ericboehlke/Resistor-Reader/resistor_pictures/0003.jpg

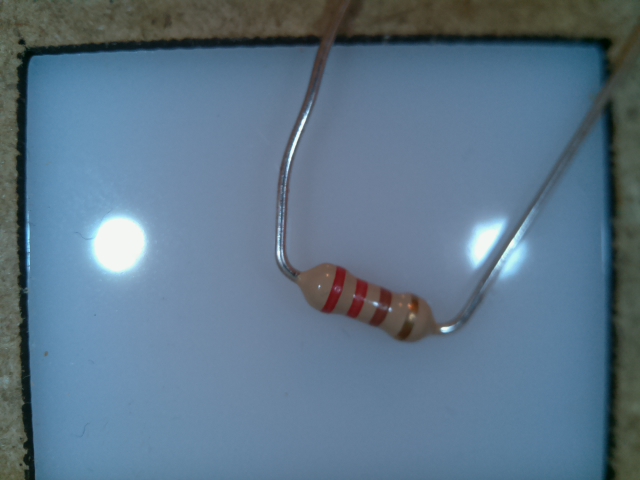
resistor_pictures/0003.jpg
