ericboehlke/Resistor-Reader/resistor_pictures/0000.jpg

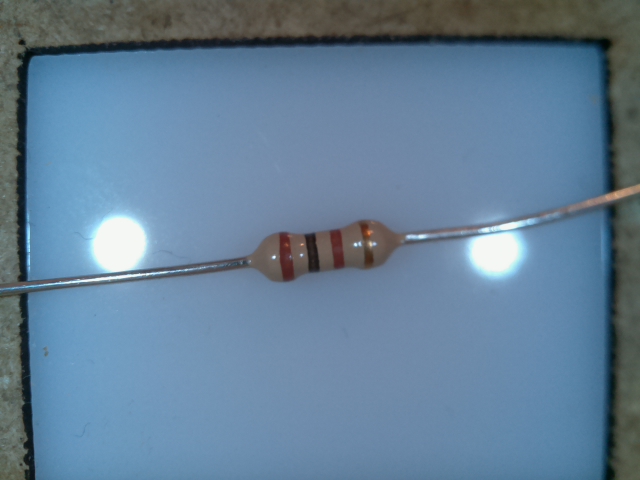
resistor_pictures/0000.jpg
