ericboehlke/Resistor-Reader/resistor_pictures/0002.jpg

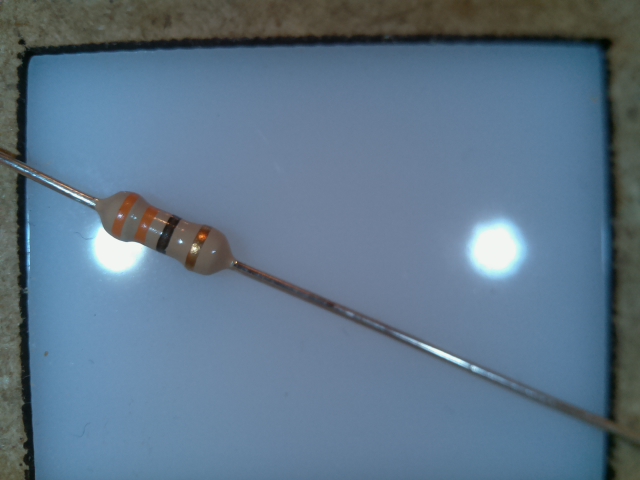
resistor_pictures/0002.jpg
