ericboehlke/Resistor-Reader/resistor_pictures/0004.jpg

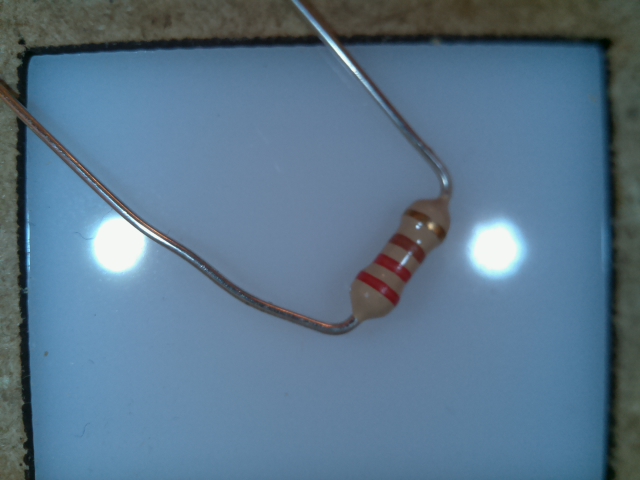
resistor_pictures/0004.jpg
