ericboehlke/Resistor-Reader/resistor_pictures/0005.jpg

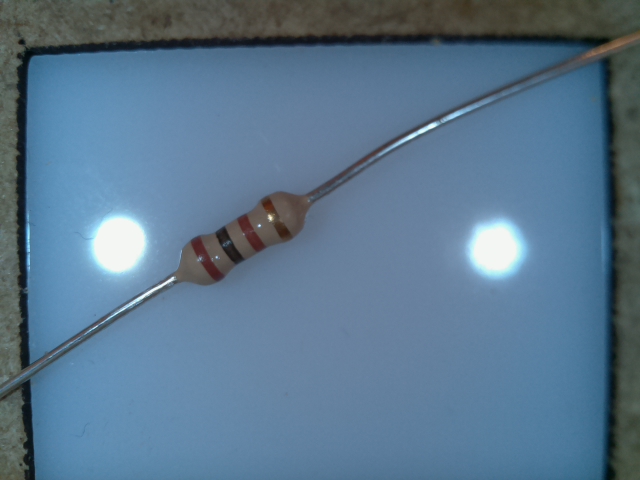
resistor_pictures/0005.jpg
