ericboehlke/Resistor-Reader/resistor_pictures/0006.jpg

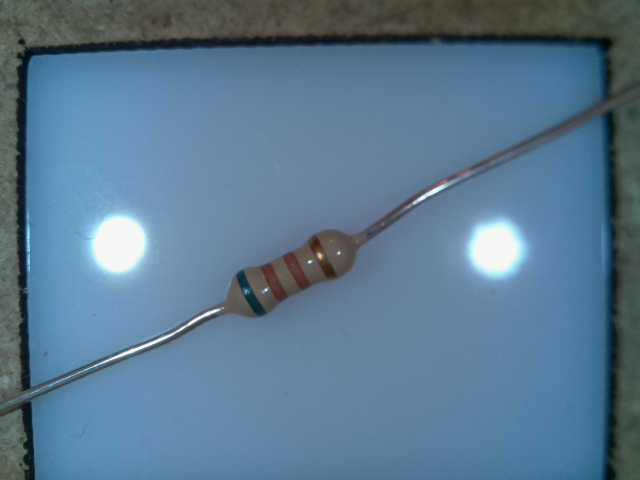
resistor_pictures/0006.jpg
