ericboehlke/Resistor-Reader/resistor_pictures/0007.jpg

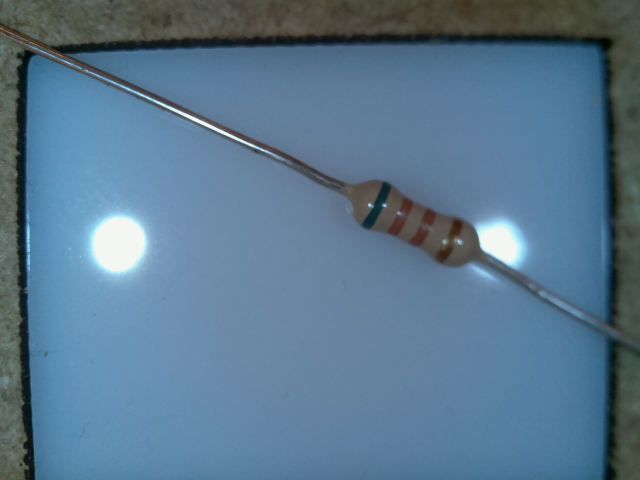
resistor_pictures/0007.jpg
