ericboehlke/Resistor-Reader/resistor_pictures/0008.jpg

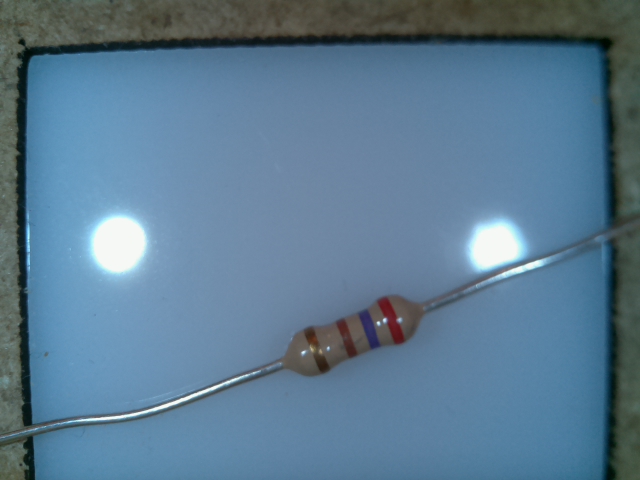
resistor_pictures/0008.jpg
