ericboehlke/Resistor-Reader/resistor_pictures/0010.jpg

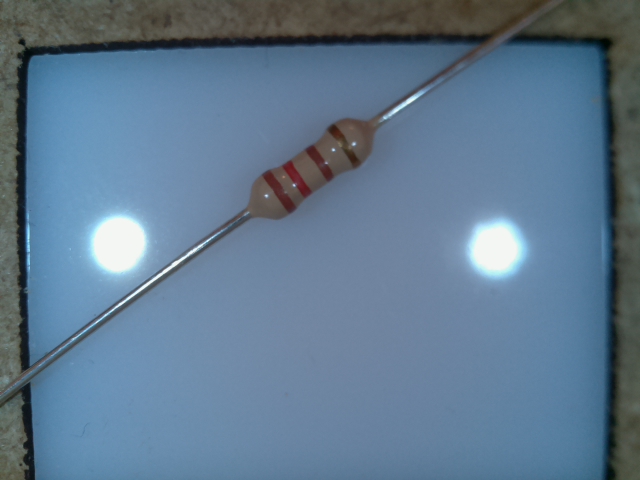
resistor_pictures/0010.jpg
