ericboehlke/Resistor-Reader/resistor_pictures/0015.jpg

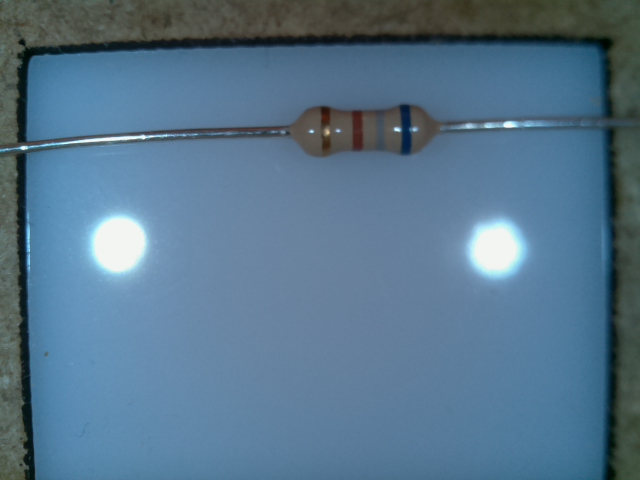
resistor_pictures/0015.jpg
