ericboehlke/Resistor-Reader/resistor_pictures/0017.jpg

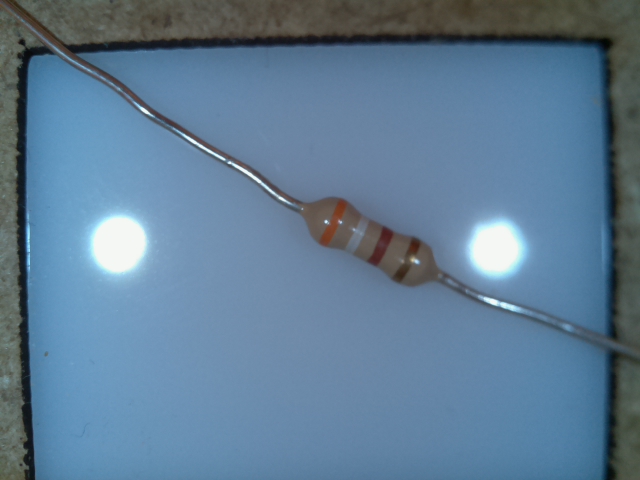
resistor_pictures/0017.jpg
