ericboehlke/Resistor-Reader/resistor_pictures/0018.jpg

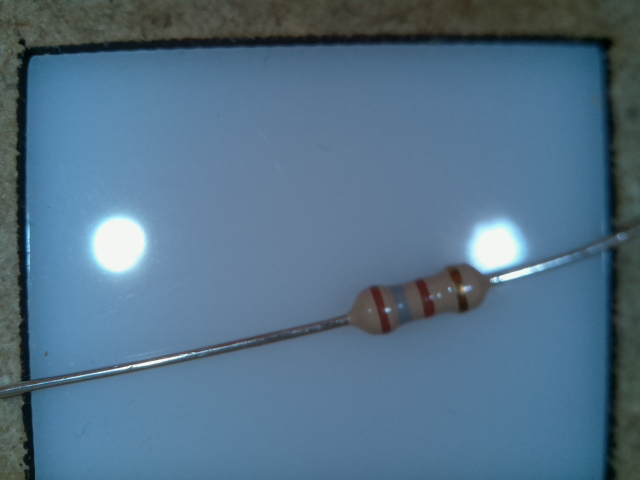
resistor_pictures/0018.jpg
