ericboehlke/Resistor-Reader/resistor_pictures/0022.jpg

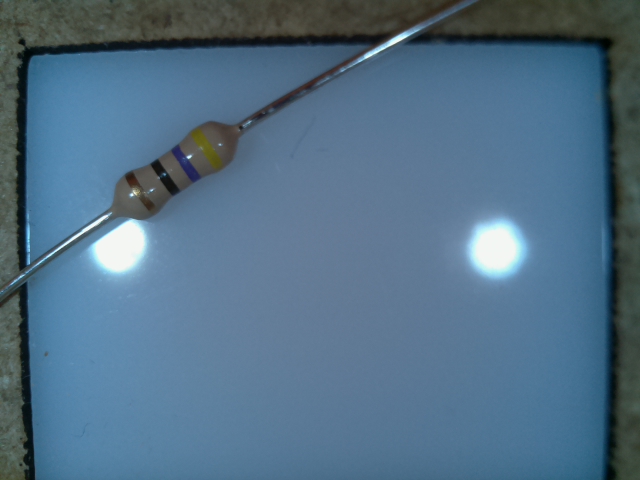
resistor_pictures/0022.jpg
