ericboehlke/Resistor-Reader/resistor_pictures/0027.jpg

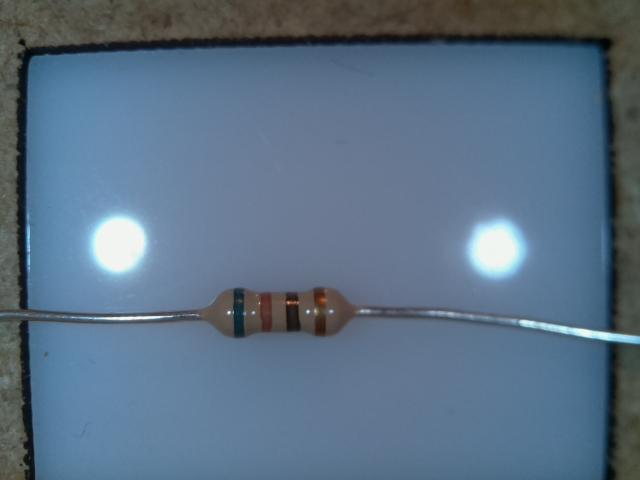
resistor_pictures/0027.jpg
