ericboehlke/Resistor-Reader/resistor_pictures/0031.jpg

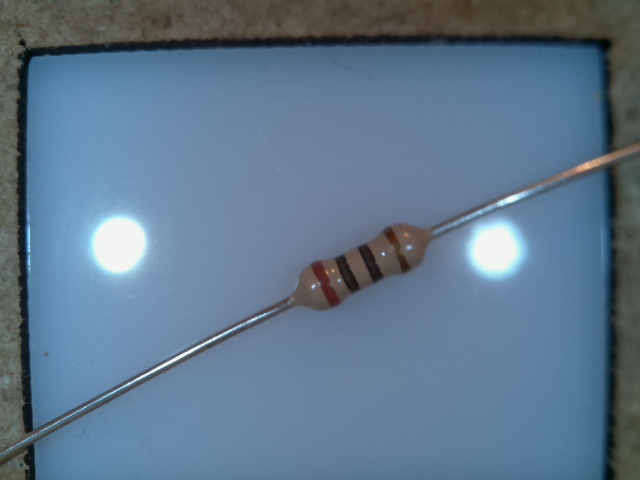
resistor_pictures/0031.jpg
