ericboehlke/Resistor-Reader/resistor_pictures/0036.jpg

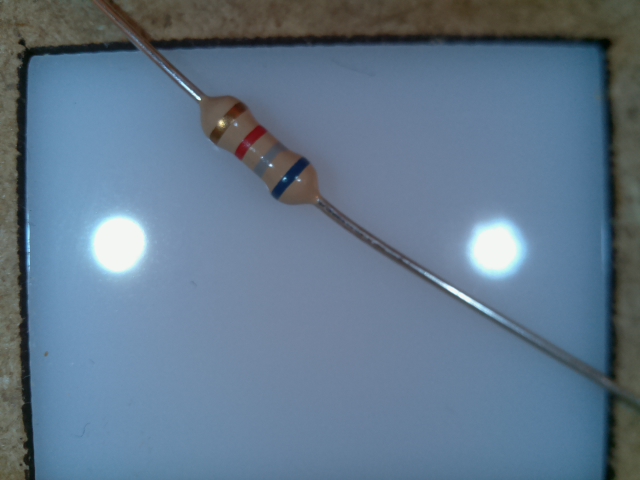
resistor_pictures/0036.jpg
