ericboehlke/Resistor-Reader/resistor_pictures/0038.jpg

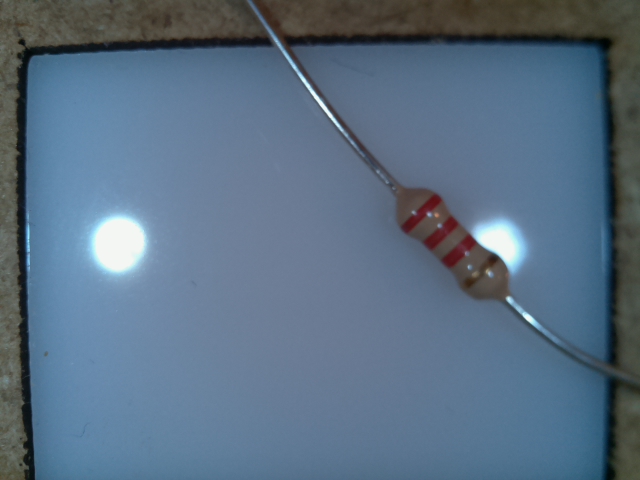
resistor_pictures/0038.jpg
