ericboehlke/Resistor-Reader/resistor_pictures/0042.jpg

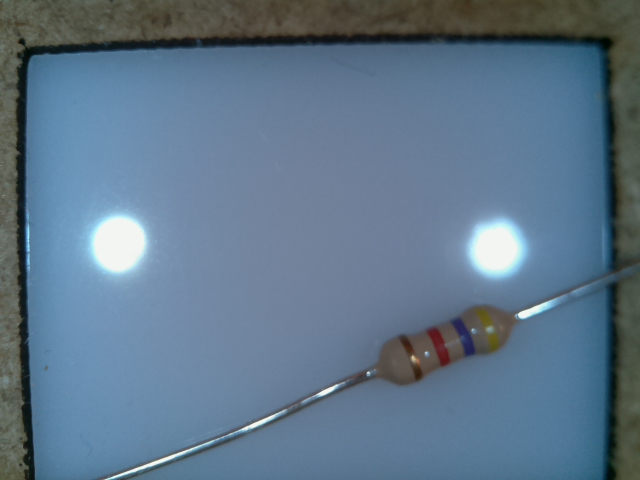
resistor_pictures/0042.jpg
