ericboehlke/Resistor-Reader/resistor_pictures/0045.jpg

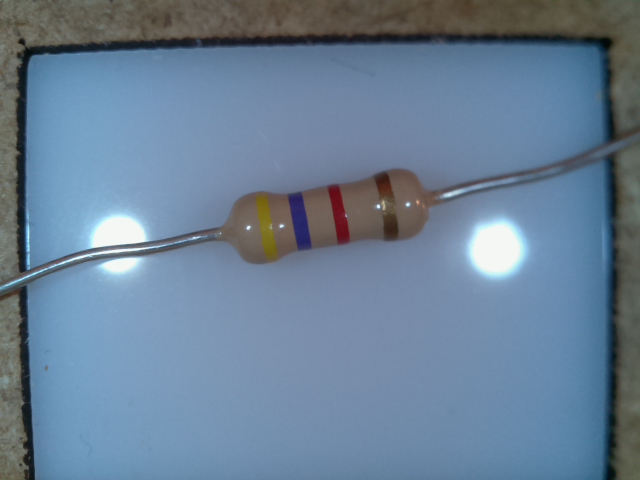
resistor_pictures/0045.jpg
