ericboehlke/Resistor-Reader/resistor_pictures/0046.jpg

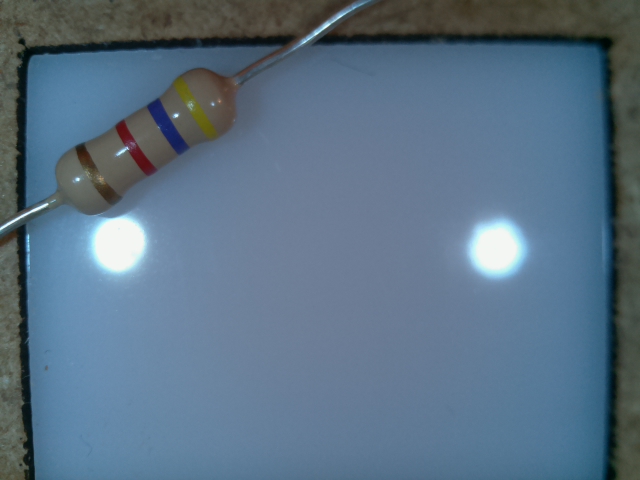
resistor_pictures/0046.jpg
