ericboehlke/Resistor-Reader/resistor_pictures/0048.jpg

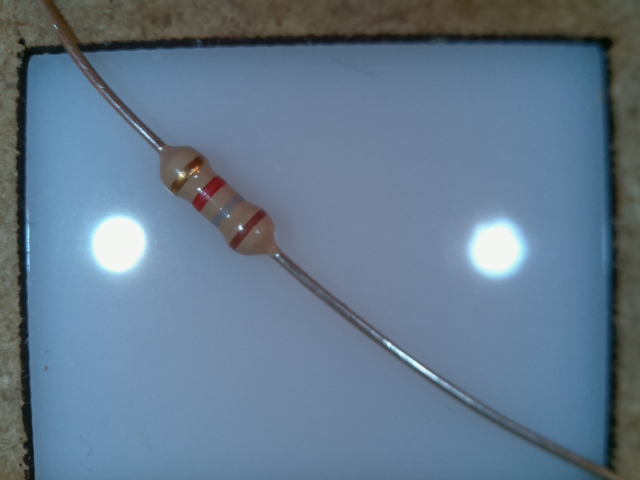
resistor_pictures/0048.jpg
