ericboehlke/Resistor-Reader/resistor_pictures/0050.jpg

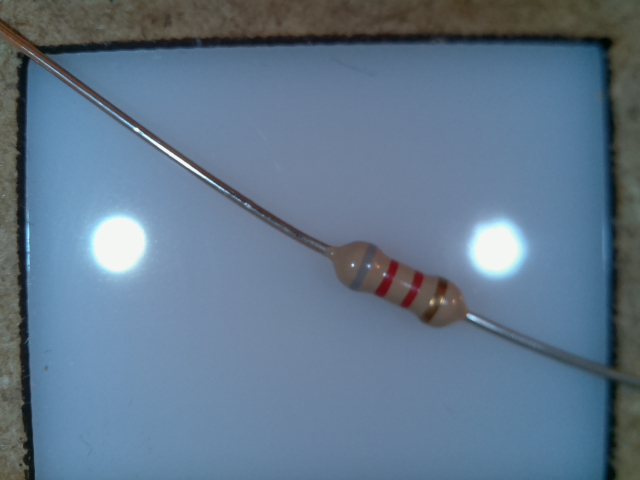
resistor_pictures/0050.jpg
