ericboehlke/Resistor-Reader/resistor_pictures/0058.jpg

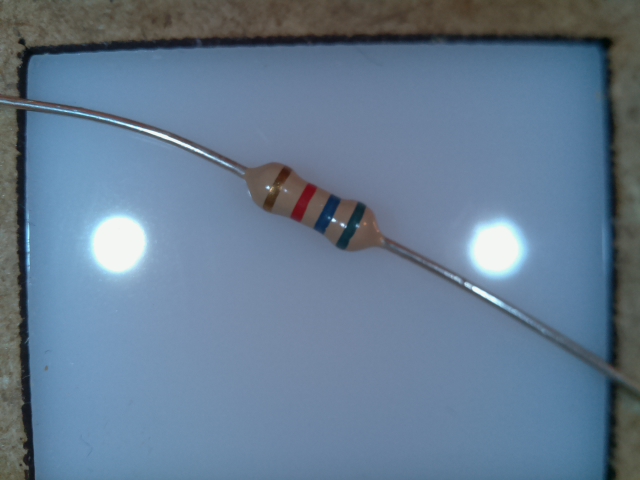
resistor_pictures/0058.jpg
