ericboehlke/Resistor-Reader/resistor_pictures/0061.jpg

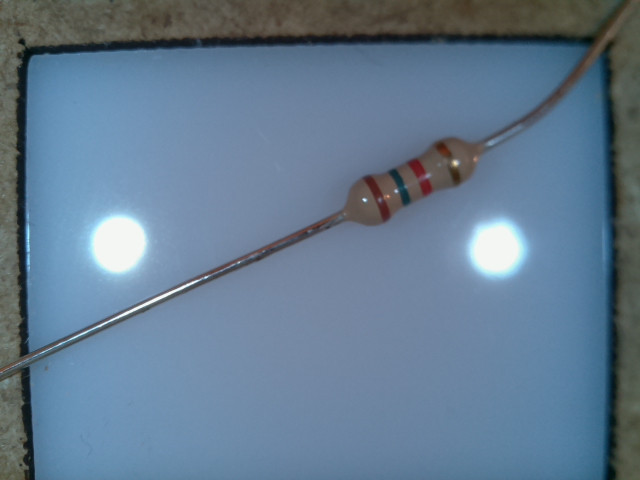
resistor_pictures/0061.jpg
