ericboehlke/Resistor-Reader/resistor_pictures/0064.jpg

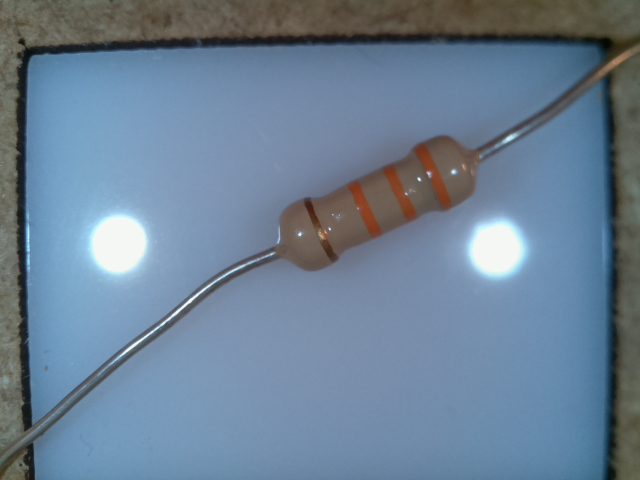
resistor_pictures/0064.jpg
