ericboehlke/Resistor-Reader/resistor_pictures/0065.jpg

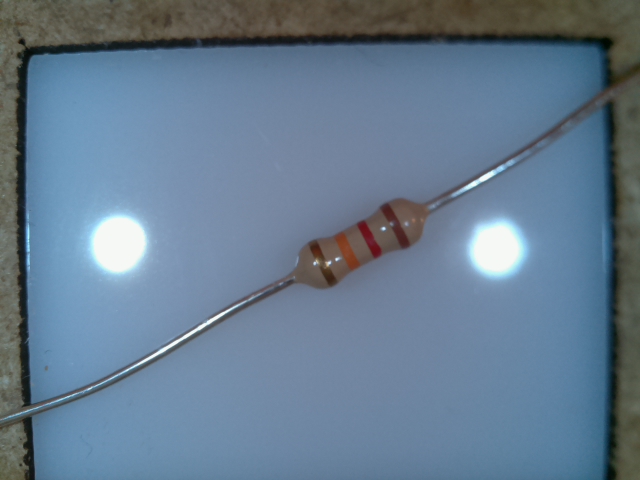
resistor_pictures/0065.jpg
