ericboehlke/Resistor-Reader/resistor_pictures/0068.jpg

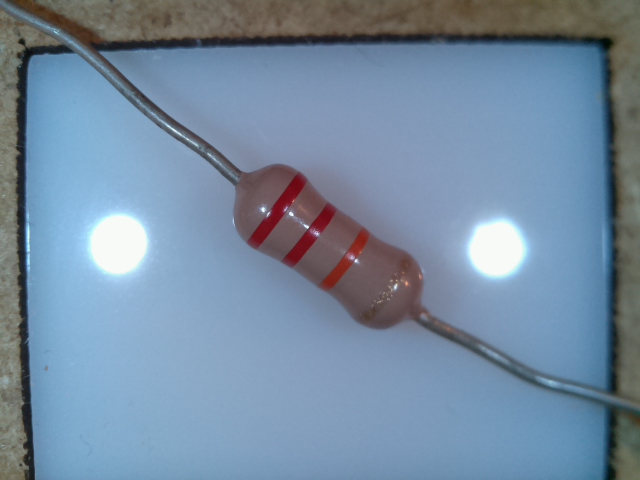
resistor_pictures/0068.jpg
