ericboehlke/Resistor-Reader/resistor_pictures/0072.jpg

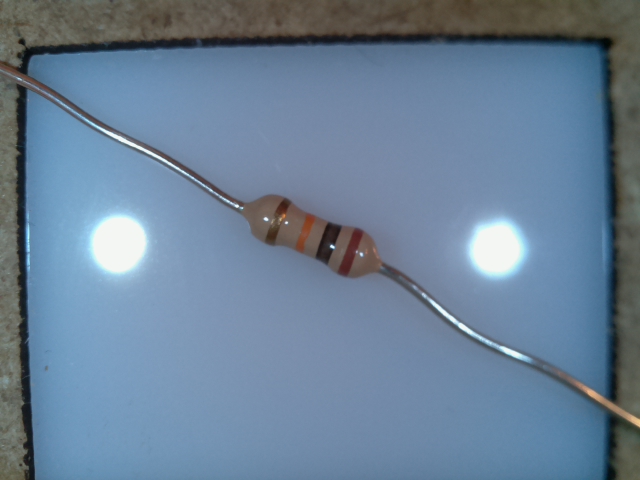
resistor_pictures/0072.jpg
