ericboehlke/Resistor-Reader/resistor_pictures/0073.jpg

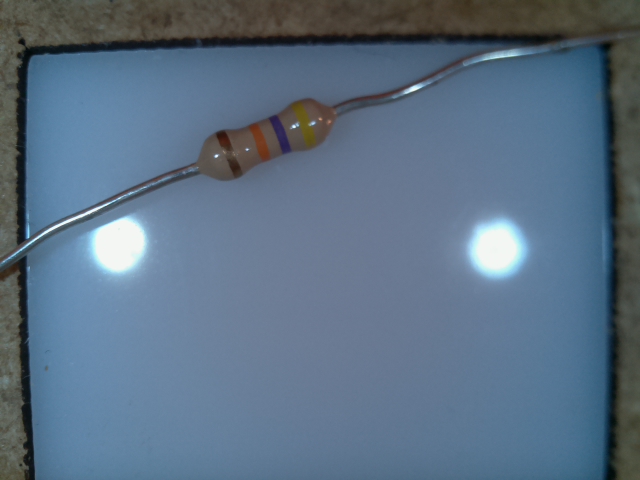
resistor_pictures/0073.jpg
