ericboehlke/Resistor-Reader/resistor_pictures/0078.jpg

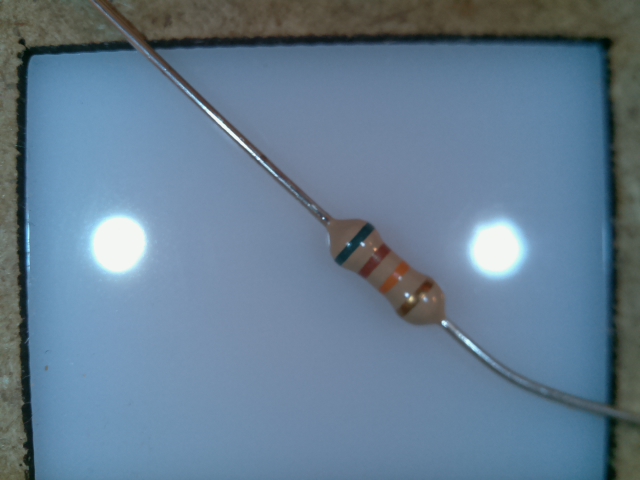
resistor_pictures/0078.jpg
