ericboehlke/Resistor-Reader/resistor_pictures/0080.jpg

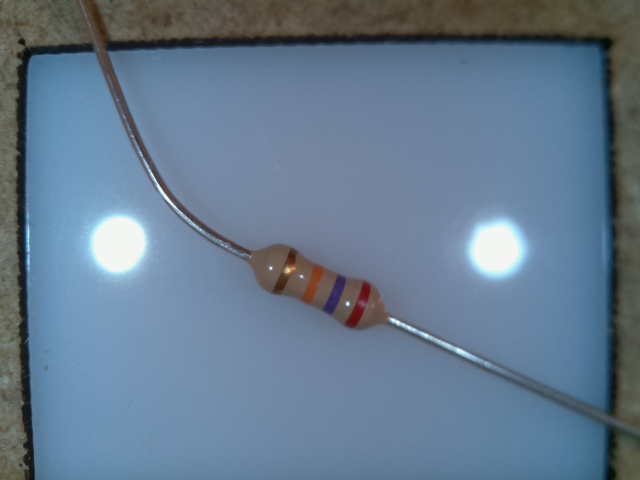
resistor_pictures/0080.jpg
