ericboehlke/Resistor-Reader/resistor_pictures/0084.jpg

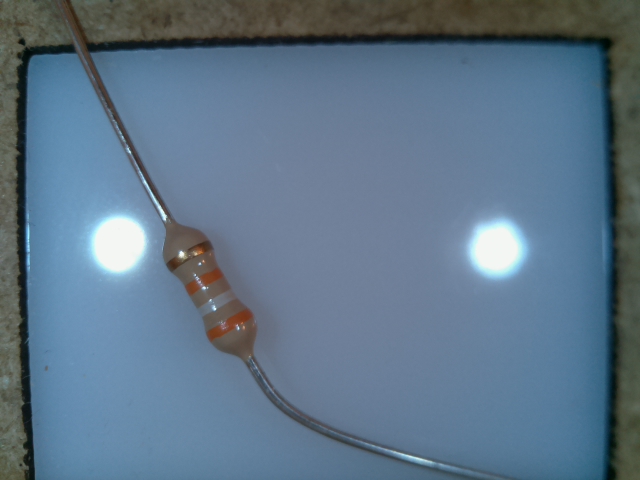
resistor_pictures/0084.jpg
