ericboehlke/Resistor-Reader/resistor_pictures/0086.jpg

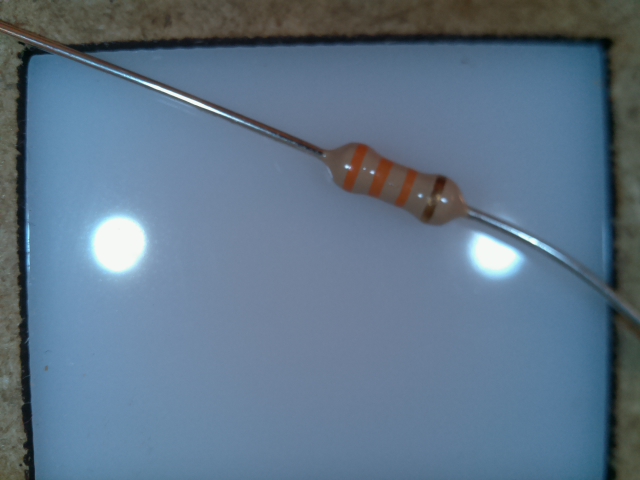
resistor_pictures/0086.jpg
