ericboehlke/Resistor-Reader/resistor_pictures/0088.jpg

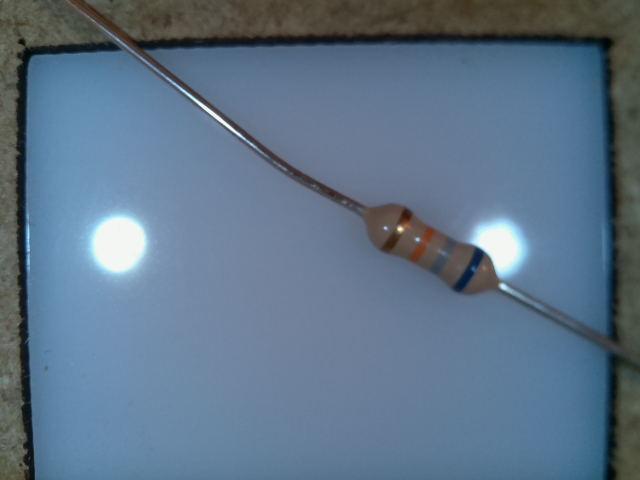
resistor_pictures/0088.jpg
