ericboehlke/Resistor-Reader/resistor_pictures/0090.jpg

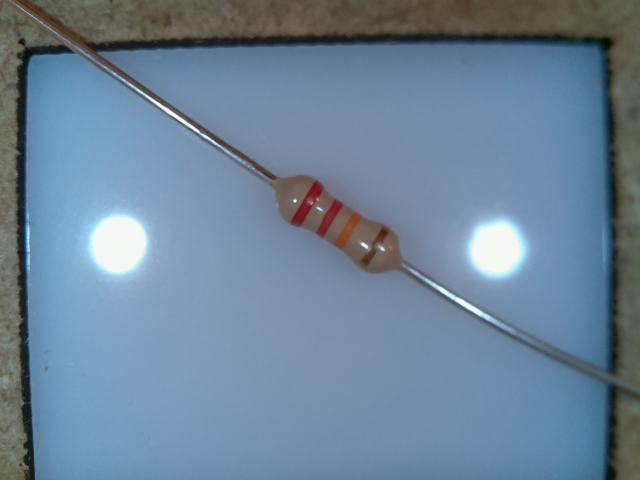
resistor_pictures/0090.jpg
