ericboehlke/Resistor-Reader/resistor_pictures/0098.jpg

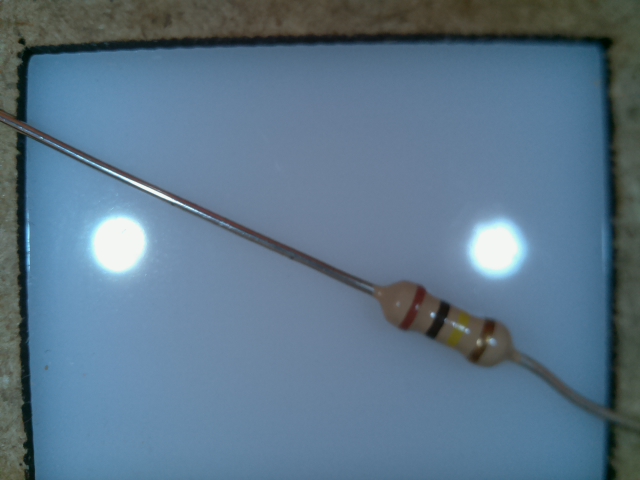
resistor_pictures/0098.jpg
