ericboehlke/Resistor-Reader/resistor_pictures/0099.jpg

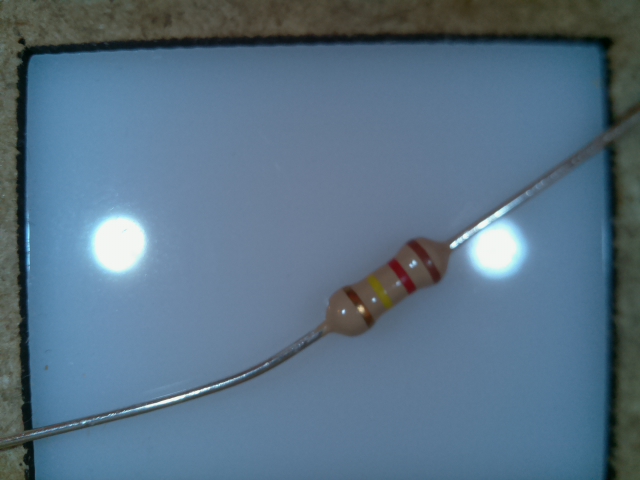
resistor_pictures/0099.jpg
