ericboehlke/Resistor-Reader/resistor_pictures/0106.jpg

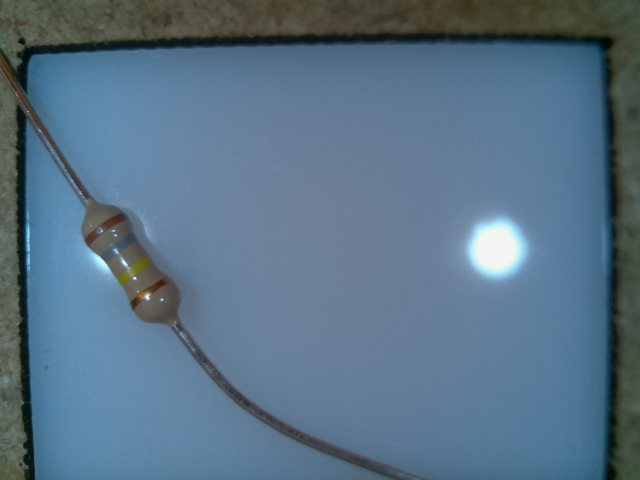
resistor_pictures/0106.jpg
