ericboehlke/Resistor-Reader/resistor_pictures/0114.jpg

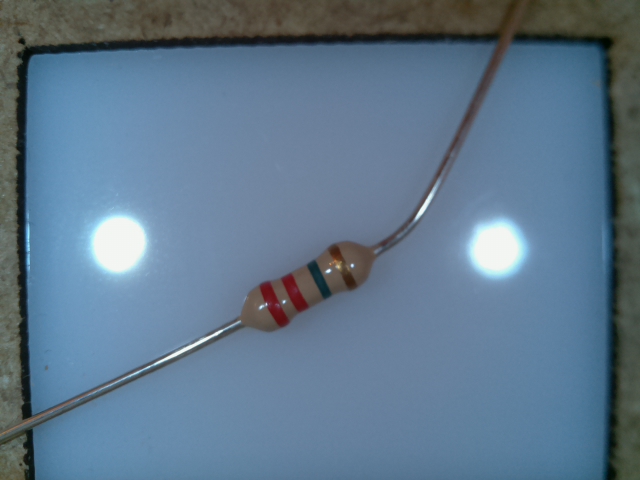
resistor_pictures/0114.jpg
