ericboehlke/Resistor-Reader/resistor_pictures/0116.jpg

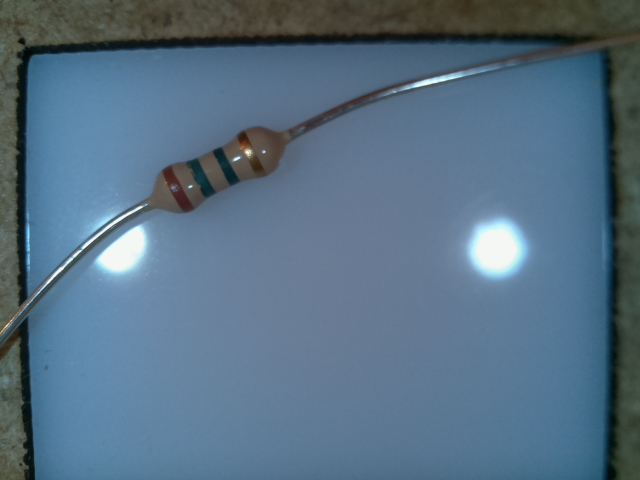
resistor_pictures/0116.jpg
