ericboehlke/Resistor-Reader/resistor_pictures/0117.jpg

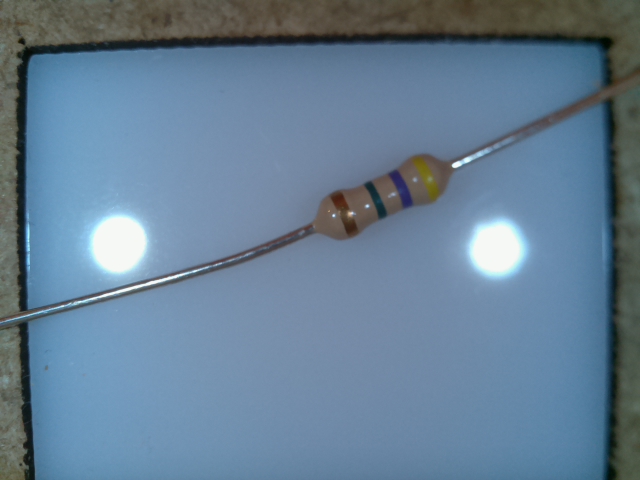
resistor_pictures/0117.jpg
