ericboehlke/Resistor-Reader/resistor_pictures/0122.jpg

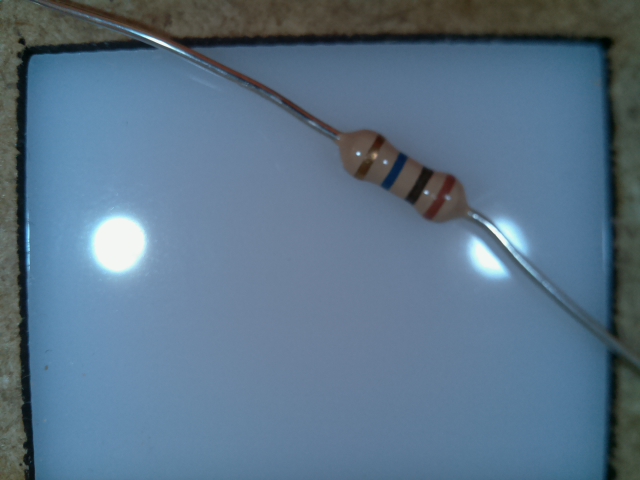
resistor_pictures/0122.jpg
