ericboehlke/Resistor-Reader/resistor_pictures/0126.jpg

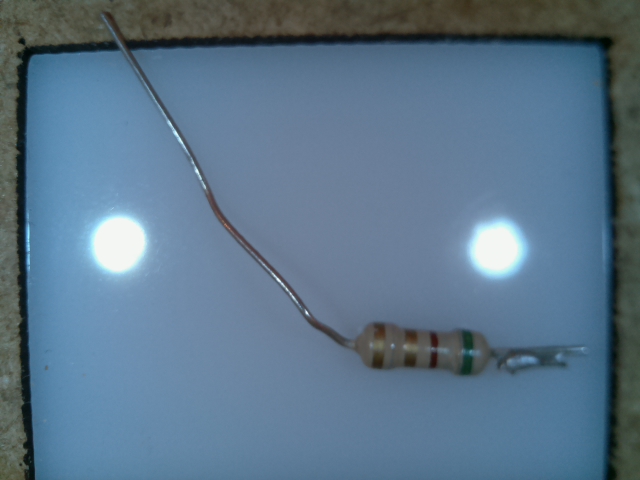
resistor_pictures/0126.jpg
