ericboehlke/Resistor-Reader/resistor_reader/decode.py

"""Constrained decoding of band color scores into a resistance value.

``classify.classify_bands`` produces a score for every color on every band instead
of a hard label.  This module searches over band order and the top few color
candidates per band, keeps only sequences that form a legal 4-band resistor
code, and returns the best-scoring one.

The structural rules are what make orientation work.  A photographed resistor
is just as likely to be tolerance-band-left as tolerance-band-right, and the
band colors themselves are the only cue to which end is which:

* the tolerance band is never black, orange, yellow or white (EIA-RS-279), so
  an end band confidently in that set cannot be the tolerance band;
* the first significant digit is never black (no leading-zero resistors);
* real parts come from the E24 preferred-value series, applied here as a bonus
  rather than a filter so an unusual part still decodes.
"""

from __future__ import annotations

from collections.abc import Iterable
from itertools import product
from typing import Any

from .models import (
    BandColorTuple,
    ColorsEnum,
    DecodeInput,
    DecodeOutput,
    ErrorCodeEnum,
)

# The color code itself: first two bands are significant digits, the third is a
# power-of-ten multiplier.  The fourth (tolerance) does not affect the value,
# but ``_sequence_prior`` uses it to work out which end is which.
DIGIT_MAP: dict[ColorsEnum, int] = {
    ColorsEnum.BLACK: 0,
    ColorsEnum.BROWN: 1,
    ColorsEnum.RED: 2,
    ColorsEnum.ORANGE: 3,
    ColorsEnum.YELLOW: 4,
    ColorsEnum.GREEN: 5,
    ColorsEnum.BLUE: 6,
    ColorsEnum.VIOLET: 7,
    ColorsEnum.GRAY: 8,
    ColorsEnum.WHITE: 9,
}

MULTIPLIER_MAP: dict[ColorsEnum, float] = {
    ColorsEnum.BLACK: 1,
    ColorsEnum.BROWN: 10,
    ColorsEnum.RED: 100,
    ColorsEnum.ORANGE: 1_000,
    ColorsEnum.YELLOW: 10_000,
    ColorsEnum.GREEN: 100_000,
    ColorsEnum.BLUE: 1_000_000,
    ColorsEnum.VIOLET: 10_000_000,
    ColorsEnum.GRAY: 100_000_000,
    ColorsEnum.WHITE: 1_000_000_000,
    ColorsEnum.GOLD: 0.1,
    ColorsEnum.SILVER: 0.01,
}

# EIA-RS-279 tolerance band colors.  Black, orange, yellow and white never
# appear as a tolerance.
TOLERANCE_COLORS: frozenset[ColorsEnum] = frozenset(
    {
        ColorsEnum.GOLD,
        ColorsEnum.SILVER,
        ColorsEnum.BROWN,
        ColorsEnum.RED,
        ColorsEnum.GREEN,
        ColorsEnum.BLUE,
        ColorsEnum.VIOLET,
        ColorsEnum.GRAY,
    }
)

# E24 preferred significant-figure pairs (IEC 60063).
E24_PAIRS: frozenset[int] = frozenset(
    {
        10, 11, 12, 13, 15, 16, 18, 20, 22, 24, 27, 30,
        33, 36, 39, 43, 47, 51, 56, 62, 68, 75, 82, 91,
    }
)


def resolve_value(colors: BandColorTuple) -> float | None:
    """Return the resistance in ohms for four ordered bands, or ``None``.

    ``None`` means the sequence is not a legal 4-band code -- a non-digit in one
    of the first two positions, or a non-multiplier in the third.
    """
    if len(colors) != 4:
        return None
    if colors[0] not in DIGIT_MAP or colors[1] not in DIGIT_MAP:
        return None
    if colors[2] not in MULTIPLIER_MAP:
        return None
    significand = DIGIT_MAP[colors[0]] * 10 + DIGIT_MAP[colors[1]]
    return float(significand * MULTIPLIER_MAP[colors[2]])


def _decode_cfg(config: dict[str, Any]) -> dict[str, Any]:
    cfg = config.get("decode", {}) or {}
    return {
        "top_k": max(1, int(cfg.get("top_k", 3))),
        "gold_tolerance_bonus": float(cfg.get("gold_tolerance_bonus", 10.0)),
        "e24_bonus": float(cfg.get("e24_bonus", 8.0)),
        "min_resistance": float(cfg.get("min_resistance", 0.1)),
        "max_resistance": float(cfg.get("max_resistance", 1e8)),
    }


def _top_candidates(
    scores: dict[ColorsEnum, float], k: int
) -> list[tuple[ColorsEnum, float]]:
    return sorted(scores.items(), key=lambda kv: kv[1], reverse=True)[:k]


def _sequence_prior(colors: BandColorTuple, cfg: dict[str, Any]) -> float | None:
    """Return the prior score for a band sequence, or ``None`` if illegal."""
    if colors[3] not in TOLERANCE_COLORS:
        return None
    if colors[0] not in DIGIT_MAP or colors[1] not in DIGIT_MAP:
        return None
    if colors[0] == ColorsEnum.BLACK:
        return None
    prior = 0.0
    if colors[3] == ColorsEnum.GOLD:
        prior += cfg["gold_tolerance_bonus"]
    pair = DIGIT_MAP[colors[0]] * 10 + DIGIT_MAP[colors[1]]
    if pair in E24_PAIRS:
        prior += cfg["e24_bonus"]
    return prior


def _hypotheses(
    scores: list[dict[ColorsEnum, float]], cfg: dict[str, Any]
) -> Iterable[tuple[float, BandColorTuple, bool]]:
    """Yield ``(score, colors, reversed_)`` for every legal band assignment."""
    for reversed_ in (False, True):
        ordered = list(reversed(scores)) if reversed_ else list(scores)
        per_band = [_top_candidates(s, cfg["top_k"]) for s in ordered]
        for combo in product(*per_band):
            colors = tuple(c for c, _ in combo)
            prior = _sequence_prior(colors, cfg)
            if prior is None:
                continue
            total = sum(v for _, v in combo) + prior
            yield total, colors, reversed_


def decode_best(stage_input: DecodeInput) -> DecodeOutput:
    """Pick the highest-scoring legal band sequence and resolve its value."""
    scores = stage_input.scores
    if len(scores) != 4:
        return DecodeOutput(
            error=ErrorCodeEnum.E04,
            error_msg=f"Expected 4 band scores, found {len(scores)}",
        )

    cfg = _decode_cfg(stage_input.config)
    best: tuple[float, BandColorTuple, bool, float] | None = None
    runner_up = float("-inf")

    for total, colors, reversed_ in _hypotheses(scores, cfg):
        value = resolve_value(colors)
        if value is None:
            continue
        if not (cfg["min_resistance"] <= value <= cfg["max_resistance"]):
            continue
        if best is None or total > best[0]:
            if best is not None and best[3] != value:
                runner_up = max(runner_up, best[0])
            best = (total, colors, reversed_, value)
        elif value != best[3]:
            runner_up = max(runner_up, total)

    if best is None:
        return DecodeOutput(
            error=ErrorCodeEnum.E04,
            error_msg="No valid band sequence.",
        )

    total, colors, reversed_, value = best
    confidence = float(total - runner_up) if runner_up > float("-inf") else float("inf")
    return DecodeOutput(
        resistance=value,
        colors=colors,
        reversed_=reversed_,
        confidence=confidence,
        _metadata={"score": total, "runner_up": runner_up},
    )
